USST-RADSAT-SK/power-and-electrical/LTSpice-TIMB/Draft1.asc

D1: zener; MMBZ6V8ALY
R1: res; 30k
R2: res
U1: SCR
Named nets: 0
.tran 11
