USST-RADSAT-SK/power-and-electrical/LTSpice-TIMB/Draft2.asc

D1: zener; MMBZ6V8ALY
R1: res; 30k
U1: SCR; EC103D1
V1: voltage; 40
Named nets: 0
.tran 10
**********
* Littelfuse, LP
* QUADRAC, SPICE Model
* Q4006LT
*
* T. Chenoski, 11/29/2007
*
**********
**********
.SUBCKT Q4006LT  1  2  3
*    TERMINALS: MT2 G MT1
Xchip1 2 4 DIAC
Xchip2 1 4 3 TRIAC
 
.SUBCKT DIAC  1   2
* TERMINALS: MT1 MT2
V1   17 3  DC 28 ac 0
V2   16 15 DC 28 ac 0
Srev 3 1 7 1  DIACtrigg  
Sfor 15 2 4 2 DIACtrigg  
Dfor 1 4 DN4148
Drev 2 7 DN4148
D1 7 17  Zone
D2 4 16  Zone
.MODEL Zone      D  (BV=100 CJO=4PF IS=7E-09 M=.45 N=.1 RS=.8 VJ=.6V)
.MODEL DN4148    D  (BV=100 CJO=4PF IS=7E-09 M=.45 N=2 RS=.8 TT=6E-09 VJ=.6V)
.MODEL DIACtrigg SW (VT=33.1 VH=5 RON=7.5 ROFF=500meg)
.ENDS
 
.SUBCKT TRIAC    1  2  3
*    TERMINALS: MT2 G MT1
Qnpn1  5 4 3  NoutF OFF
Qpnp1  4 5 7  PoutF OFF
Qnpn2 11 6 7  NoutR OFF
Qpnp2 6 11 3  PoutR OFF
Dfor  4  5 DZ OFF
Drev  6 11 DZ OFF
Rfor  4 6  12MEG
Ron   1 7  61.6M
Rhold 7 6  50
RGP   8 3  50
RG    2 8  5.8
RS    8 4  100
DN    9 2  DIN OFF
RN    9 3  6.12
GNN   6 7 9 3 1.100
GNP   4 5 9 3 0.521
DP    2 10  DIP OFF
RP    10 3  3.56
GP    7 6 10 3 0.1
.MODEL DIN   D   (IS=382F)
.MODEL DIP   D   (IS=382F N=1.19)
.MODEL DZ    D   (IS=382F N=1.5 IBV=50U BV=200)
.MODEL PoutF PNP (IS=382F BF=1 CJE=761P TF=0.3U)
.MODEL NoutF NPN (IS=382F BF=3 CJE=761P CJC=152P TF=0.3U)
.MODEL PoutR PNP (IS=382F BF=5 CJE=761P TF=0.3U)
.MODEL NoutR NPN (IS=382F BF=0.5 CJE=761P CJC=152P TF=0.3U)
.ENDS
.ENDS
**********
**********************************
**********************************
**
** Littelfuse, LP
** SCR SPICE Models
** EC103xx-SxSx
**
** T. Chenoski
** Irving Technical Center
**
** A 06/13/08
**
**********************************
**********************************
.SUBCKT EC103D1    1  2             3
*       TERMINALS: A  G             K
Qpnp    6          4  1             Pfor      OFF
Qnpn    4          6  5             Nfor      OFF
Rfor    6          4  5G
Rrev    1          4  5G
Rshort  6          5  1MEG
Rlat    2          6  9.09
Ron     3          5  513.4m
Dfor    6          4  Zbrk
Drev    1          4  Zbrk
Dgate   6          5  Zgate
.MODEL  Zbrk       D  (IS=3.2E-16   IBV=100U  BV=400)
.MODEL  Zgate      D  (IS=1E-16     IBV=100U  BV=10      VJ=0.3)
.MODEL  Pfor       PNP(IS=5E-15     BF=6.10   CJE=5p     CJC=2p     TF=0.3U)
.MODEL  Nfor       NPN(IS=1E-12     ISE=1E-9  BF=10.0    RC=0.45    CJE=30p     CJC=2p      TF=0.3U)
.ENDS
 
.SUBCKT EC103M1    1  2             3
*       TERMINALS: A  G             K
Qpnp    6          4  1             Pfor      OFF
Qnpn    4          6  5             Nfor      OFF
Rfor    6          4  5G
Rrev    1          4  5G
Rshort  6          5  1MEG
Rlat    2          6  9.09
Ron     3          5  513.4m
Dfor    6          4  Zbrk
Drev    1          4  Zbrk
Dgate   6          5  Zgate
.MODEL  Zbrk       D  (IS=3.2E-16   IBV=100U  BV=600)
.MODEL  Zgate      D  (IS=1E-16     IBV=100U  BV=10      VJ=0.3)
.MODEL  Pfor       PNP(IS=5E-15     BF=6.10   CJE=5p     CJC=2p     TF=0.3U)
.MODEL  Nfor       NPN(IS=1E-12     ISE=1E-9  BF=10.0    RC=0.45    CJE=30p     CJC=2p      TF=0.3U)
.ENDS
 
.SUBCKT EC103D2    1  2             3
*       TERMINALS: A  G             K
Qpnp    6          4  1             Pfor      OFF
Qnpn    4          6  5             Nfor      OFF
Rfor    6          4  5G
Rrev    1          4  5G
Rshort  6          5  1MEG
Rlat    2          6  9.09
Ron     3          5  513.4m
Dfor    6          4  Zbrk
Drev    1          4  Zbrk
Dgate   6          5  Zgate
.MODEL  Zbrk       D  (IS=3.2E-16   IBV=100U  BV=400)
.MODEL  Zgate      D  (IS=1E-16     IBV=100U  BV=10      VJ=0.3)
.MODEL  Pfor       PNP(IS=5E-15     BF=2.20   CJE=5p     CJC=2p     TF=0.3U)
.MODEL  Nfor       NPN(IS=1E-12     ISE=1E-9  BF=10.0    RC=0.45    CJE=30p     CJC=2p      TF=0.3U)
.ENDS
 
.SUBCKT EC103M2    1  2             3
*       TERMINALS: A  G             K
Qpnp    6          4  1             Pfor      OFF
Qnpn    4          6  5             Nfor      OFF
Rfor    6          4  5G
Rrev    1          4  5G
Rshort  6          5  1MEG
Rlat    2          6  9.09
Ron     3          5  513.4m
Dfor    6          4  Zbrk
Drev    1          4  Zbrk
Dgate   6          5  Zgate
.MODEL  Zbrk       D  (IS=3.2E-16   IBV=100U  BV=600)
.MODEL  Zgate      D  (IS=1E-16     IBV=100U  BV=10      VJ=0.3)
.MODEL  Pfor       PNP(IS=5E-15     BF=2.20   CJE=5p     CJC=2p     TF=0.3U)
.MODEL  Nfor       NPN(IS=1E-12     ISE=1E-9  BF=10.0    RC=0.45    CJE=30p     CJC=2p      TF=0.3U)
.ENDS
 
.SUBCKT EC103D     1  2             3
*       TERMINALS: A  G             K
Qpnp    6          4  1             Pfor      OFF
Qnpn    4          6  5             Nfor      OFF
Rfor    6          4  5G
Rrev    1          4  5G
Rshort  6          5  1MEG
Rlat    2          6  9.09
Ron     3          5  513.4m
Dfor    6          4  Zbrk
Drev    1          4  Zbrk
Dgate   6          5  Zgate
.MODEL  Zbrk       D  (IS=3.2E-16   IBV=100U  BV=400)
.MODEL  Zgate      D  (IS=1E-16     IBV=100U  BV=10      VJ=0.3)
.MODEL  Pfor       PNP(IS=5E-15     BF=1.10   CJE=5p     CJC=2p     TF=0.3U)
.MODEL  Nfor       NPN(IS=1E-12     ISE=1E-9  BF=10.0    RC=0.45    CJE=30p     CJC=2p      TF=0.3U)
.ENDS
 
.SUBCKT EC103M     1  2             3
*       TERMINALS: A  G             K
Qpnp    6          4  1             Pfor      OFF
Qnpn    4          6  5             Nfor      OFF
Rfor    6          4  5G
Rrev    1          4  5G
Rshort  6          5  1MEG
Rlat    2          6  9.09
Ron     3          5  513.4m
Dfor    6          4  Zbrk
Drev    1          4  Zbrk
Dgate   6          5  Zgate
.MODEL  Zbrk       D  (IS=3.2E-16   IBV=100U  BV=600)
.MODEL  Zgate      D  (IS=1E-16     IBV=100U  BV=10      VJ=0.3)
.MODEL  Pfor       PNP(IS=5E-15     BF=1.10   CJE=5p     CJC=2p     TF=0.3U)
.MODEL  Nfor       NPN(IS=1E-12     ISE=1E-9  BF=10.0    RC=0.45    CJE=30p     CJC=2p      TF=0.3U)
.ENDS
 
.SUBCKT EC103D3    1  2             3
*       TERMINALS: A  G             K
Qpnp    6          4  1             Pfor      OFF
Qnpn    4          6  5             Nfor      OFF
Rfor    6          4  5G
Rrev    1          4  5G
Rshort  6          5  1MEG
Rlat    2          6  9.09
Ron     3          5  513.4m
Dfor    6          4  Zbrk
Drev    1          4  Zbrk
Dgate   6          5  Zgate
.MODEL  Zbrk       D  (IS=3.2E-16   IBV=100U  BV=400)
.MODEL  Zgate      D  (IS=1E-16     IBV=100U  BV=10      VJ=0.3)
.MODEL  Pfor       PNP(IS=5E-15     BF=0.95   CJE=5p     CJC=2p     TF=0.3U)
.MODEL  Nfor       NPN(IS=1E-12     ISE=1E-9  BF=10.0    RC=0.45    CJE=30p     CJC=2p      TF=0.3U)
.ENDS
 
.SUBCKT EC103M3    1  2             3
*       TERMINALS: A  G             K
Qpnp    6          4  1             Pfor      OFF
Qnpn    4          6  5             Nfor      OFF
Rfor    6          4  5G
Rrev    1          4  5G
Rshort  6          5  1MEG
Rlat    2          6  9.09
Ron     3          5  513.4m
Dfor    6          4  Zbrk
Drev    1          4  Zbrk
Dgate   6          5  Zgate
.MODEL  Zbrk       D  (IS=3.2E-16   IBV=100U  BV=600)
.MODEL  Zgate      D  (IS=1E-16     IBV=100U  BV=10      VJ=0.3)
.MODEL  Pfor       PNP(IS=5E-15     BF=0.95   CJE=5p     CJC=2p     TF=0.3U)
.MODEL  Nfor       NPN(IS=1E-12     ISE=1E-9  BF=10.0    RC=0.45    CJE=30p     CJC=2p      TF=0.3U)
.ENDS
 
.SUBCKT S4S1       1  2             3
*       TERMINALS: A  G             K
Qpnp    6          4  1             Pfor      OFF
Qnpn    4          6  5             Nfor      OFF
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
Rfor    6          4  5G
Rrev    1          4  5G
Rshort  6          5  1MEG
Rlat    2          6  9.09
Ron     3          5  513.4m
Dfor    6          4  Zbrk
Drev    1          4  Zbrk
Dgate   6          5  Zgate
.MODEL  Zbrk       D  (IS=3.2E-16   IBV=100U  BV=400)
.MODEL  Zgate      D  (IS=1E-16     IBV=100U  BV=10      VJ=0.3)
.MODEL  Pfor       PNP(IS=5E-15     BF=0.95   CJE=5p     CJC=2p     TF=0.3U)
.MODEL  Nfor       NPN(IS=1E-12     ISE=1E-9  BF=10.0    RC=0.45    CJE=30p     CJC=2p      TF=0.3U)
.ENDS
 
.SUBCKT S6S3       1  2             3
*       TERMINALS: A  G             K
Qpnp    6          4  1             Pfor      OFF
Qnpn    4          6  5             Nfor      OFF
Rfor    6          4  5G
Rrev    1          4  5G
Rshort  6          5  1MEG
Rlat    2          6  9.09
Ron     3          5  513.4m
Dfor    6          4  Zbrk
Drev    1          4  Zbrk
Dgate   6          5  Zgate
.MODEL  Zbrk       D  (IS=3.2E-16   IBV=100U  BV=600)
.MODEL  Zgate      D  (IS=1E-16     IBV=100U  BV=10      VJ=0.3)
.MODEL  Pfor       PNP(IS=5E-15     BF=0.95   CJE=5p     CJC=2p     TF=0.3U)
.MODEL  Nfor       NPN(IS=1E-12     ISE=1E-9  BF=10.0    RC=0.45    CJE=30p     CJC=2p      TF=0.3U)
.ENDS
