USST-RADSAT-SK/power-and-electrical/LTSpice-TIMB/RBF_Buck_Booster.asc

C1: cap; 22µ; Rser=0.002
C2: cap; 0.1µ
C3: cap; 10µ
C4: cap; 1.5n
D1: schottky; PMEG2010EA
D2: zener; BZX84C6V2L; 0; 1
L1: ind; 10µ; Ipk=1 Rser=0.226 Rpar=942 Cpar=0 mfg="Coilcraft" pn="DO1606T-103"
M1: nmos; irlml2060pbf
M2: nmos; irlml2060pbf
M3: nmos; irlml2060pbf
R1: res; 60.4K
R2: res; 619k
R4: res; 1000000
R5: res; 200k
R6: res; 15k
R7: res; 3000000
R8: res; 100
R9: res; 1000000
R10: res; 100
U1: LTC3440
V1: voltage; 3
Named nets: 0, +BATT, 1, 2
.inc irfl4310.spi
.tran 0 699 0 10000 startup
.SUBCKT irlml2060pbf 1 2 3
* SPICE3 MODEL WITH THERMAL RC NETWORK
**************************************
*      Model Generated by MODPEX     *
*Copyright(c) Symmetry Design Systems*
*         All Rights Reserved        *
*    UNPUBLISHED LICENSED SOFTWARE   *
*   Contains Proprietary Information *
*      Which is The Property of      *
*     SYMMETRY OR ITS LICENSORS      *
*Commercial Use or Resale Restricted *
*   by Symmetry License Agreement    *
**************************************
* Model generated on Aug 16, 10
* MODEL FORMAT: SPICE3
* Symmetry POWER MOS Model (Version 1.0)
* External Node Designations
* Node 1 -> Drain
* Node 2 -> Gate
* Node 3 -> Source
M1 9 7 8 8 MM L=100u W=100u
.MODEL MM NMOS LEVEL=1 IS=1e-32
+VTO=2.80157 LAMBDA=0.0343822 KP=4.48896
+CGSO=5.8563e-07 CGDO=1.50373e-08
RS 8 3 0.330834
D1 3 1 MD
.MODEL MD D IS=1.4393e-09 RS=0.0402678 N=1.5 BV=60
+IBV=0.00025 EG=1 XTI=1 TT=1e-07
+CJO=4.47874e-11 VJ=0.5 M=0.519102 FC=0.5
RDS 3 1 1e+07
RD 9 1 0.0274132
RG 2 7 17.3855
D2 4 5 MD1
* Default values used in MD1:
*   RS=0 EG=1.11 XTI=3.0 TT=0
*   BV=infinite IBV=1mA
.MODEL MD1 D IS=1e-32 N=50
+CJO=1.66547e-11 VJ=0.5 M=0.3 FC=1e-08
D3 0 5 MD2
* Default values used in MD2:
*   EG=1.11 XTI=3.0 TT=0 CJO=0
*   BV=infinite IBV=1mA
.MODEL MD2 D IS=1e-10 N=0.4 RS=3e-06
RL 5 10 1
FI2 7 9 VFI2 -1
VFI2 4 0 0
EV16 10 0 9 7 1
CAP 11 10 4.56066e-11
FI1 7 9 VFI1 -1
VFI1 11 6 0
RCAP 6 10 1
D4 0 6 MD3
* Default values used in MD3:
*   EG=1.11 XTI=3.0 TT=0 CJO=0
*   RS=0 BV=infinite IBV=1mA
.MODEL MD3 D IS=1e-10 N=0.4
.ENDS irlml2060pbf
*SPICE Thermal Model Subcircuit
.SUBCKT irlml2060pbft 5 1
 
R_RTHERM1         5 4  4.663e+00
R_RTHERM2         4 3  4.216e+01
R_RTHERM3         3 2  3.481e+01
R_RTHERM4         2 1  1.832e+01
C_CTHERM1         5 1  3.165e-05
C_CTHERM2         4 1  1.524e-03
C_CTHERM3         3 1  1.125e-02
C_CTHERM4         2 1  3.319e-04
 
.ENDS irlml2060pbft
.SUBCKT irfl4310 1 2 3
**************************************
*      Model Generated by MODPEX     *
*Copyright(c) Symmetry Design Systems*
*         All Rights Reserved        *
*    UNPUBLISHED LICENSED SOFTWARE   *
*   Contains Proprietary Information *
*      Which is The Property of      *
*     SYMMETRY OR ITS LICENSORS      *
*Commercial Use or Resale Restricted *
*   by Symmetry License Agreement    *
**************************************
* Model generated on Nov 20, 01
* MODEL FORMAT: SPICE3
* Symmetry POWER MOS Model (Version 1.0)
* External Node Designations
* Node 1 -> Drain
* Node 2 -> Gate
* Node 3 -> Source
M1 9 7 8 8 MM L=100u W=100u
.MODEL MM NMOS LEVEL=1 IS=1e-32
+VTO=3.58936 LAMBDA=0.000801004 KP=6.35786
+CGSO=2.7e-06 CGDO=1.75409e-07
RS 8 3 0.0864378
D1 3 1 MD
.MODEL MD D IS=5.09176e-15 RS=0.0287852 N=0.898689 BV=100
+IBV=0.00025 EG=1 XTI=4 TT=0.0001
+CJO=1.70375e-10 VJ=1.2893 M=0.492492 FC=0.5
RDS 3 1 1e+06
RD 9 1 0.0655086
RG 2 7 14.0675
D2 4 5 MD1
* Default values used in MD1:
*   RS=0 EG=1.11 XTI=3.0 TT=0
*   BV=infinite IBV=1mA
.MODEL MD1 D IS=1e-32 N=50
+CJO=4.26402e-10 VJ=0.5 M=0.631994 FC=1e-08
D3 0 5 MD2
* Default values used in MD2:
*   EG=1.11 XTI=3.0 TT=0 CJO=0
*   BV=infinite IBV=1mA
.MODEL MD2 D IS=1e-10 N=0.4 RS=3e-06
RL 5 10 1
FI2 7 9 VFI2 -1
VFI2 4 0 0
EV16 10 0 9 7 1
CAP 11 10 9.53251e-10
FI1 7 9 VFI1 -1
VFI1 11 6 0
RCAP 6 10 1
D4 0 6 MD3
* Default values used in MD3:
*   EG=1.11 XTI=3.0 TT=0 CJO=0
*   RS=0 BV=infinite IBV=1mA
.MODEL MD3 D IS=1e-10 N=0.4
.ENDS irfl4310
