USST-RADSAT-SK/power-and-electrical/LTSpice-TIMB_2/Current-divider.asc

I1: current; 300mA
R1: res; 9170
R2: res; 10.4k
R3: res; 10
Named nets: 0
.tran 2
