USST-RADSAT-SK/power-and-electrical/LTSpice-TIMB_2/LT1521.asc

C1: cap; 1.5µ
R1: res; 2k
R2: res; 11k
R3: res; 200
R4: res; 100
Rload: res; 1
U1: LT1521
V1: voltage; PWL(0 0 1 5)
Named nets: 0, IN, OUT
.tran 10
