USST-RADSAT-SK/power-and-electrical/LTSpice-TIMB_2/RBF_Logic.asc

C1: polcap; 0.01µ
C2: polcap; 470µ
C3: polcap; 470µ
C4: polcap; 0.01µ
C5: polcap; 470µ
C6: polcap; 0.01µ
C7: cap; 12
C8: cap; 12
R1: res; 2500000
R2: res; 100
R3: res; 2500000
R4: res; 2500000
R5: res; 2500000
R6: res; 100
R7: res; 2500000
R8: res; 2500000
R9: res; 100
R10: res; 100
R11: res; 100
U1: NE555
U2: NE555
U3: NE555
V1: voltage; 3
V2: voltage; 3
Named nets: 5V_charge, 0, output_3, output_1, output_2
Switch
Switch
Switch
<- Switch (open when RBF is inserted)
RBF->
.tran 0 3600 0 100
