USST-RADSAT-SK/power-and-electrical/LTSpice-TIMB_2/timer_chip.asc

C1: cap; 680µ
R1: res; 3000k
V2: voltage; 3
Named nets: 0, output
.tran 0 7200 0 100
