USST-RADSAT-SK/power-and-electrical/RADSAT-SK_timer_2/LTSpice-TIMB/Enable_RBF_logic.asc

D1: schottky; BAT54
D2: schottky; BAT54
D3: LED; NSPW500BS
D4: diode
D5: diode
D6: diode
M1: nmos
M2: nmos
M3: nmos
R1: res; 100
R2: res; 1k
R3: res; 1k
R4: res; 1000
R5: res; 100
R6: res; 100
R7: res; 1000
S1: sw
S2: sw
S3: sw
V1: voltage; 5
V2: voltage; 4.5
Named nets: 0, Inhib_EN, 2, 1
.model SW SW()
.tran 50ms
