USST-RADSAT-SK/power-and-electrical/RADSAT-SK_timer_2/LTSpice-TIMB/RBF_logic_Batt_Board.asc

D1: schottky; BAT54
D2: schottky; BAT54
D3: LED; W5AP-LZMZ-5K8L
D4: diode
R1: res; 1k
R3: res; 1k
S1: sw
V1: voltage; 5
V2: voltage; 5
Named nets: +BATT, 0, InhibitV+
.tran 50ms
.model SW SW()
