USST-RADSAT-SK/power-and-electrical/RADSAT-SK_timer_2/LTSpice-TIMB/Buck_booster.asc

C1: cap; 10µ
C2: cap; 1.5n
C3: cap; 22µ; Rser=0.002
C4: cap; 0.1µ
D1: schottky; BAT54
L1: ind; 10µ; Ipk=1 Rser=0.226 Rpar=942 Cpar=0 mfg="Coilcraft" pn="DO1606T-103"
R1: res; 60.4K
R2: res; 200k
R3: res; 15k
R4: res; 619k
R5: res; 100
R6: res; 1000k
U1: LTC3440
V1: voltage; 5V
V2: voltage; 4.5V
Named nets: 0, +5V, +BATT, Vin
;tran 10ms
.inc irfl4310.spi
.tran 6ms
